tomomo086/3D_Storage_Box_System/Images/IMG_20250630_092257031.JPG

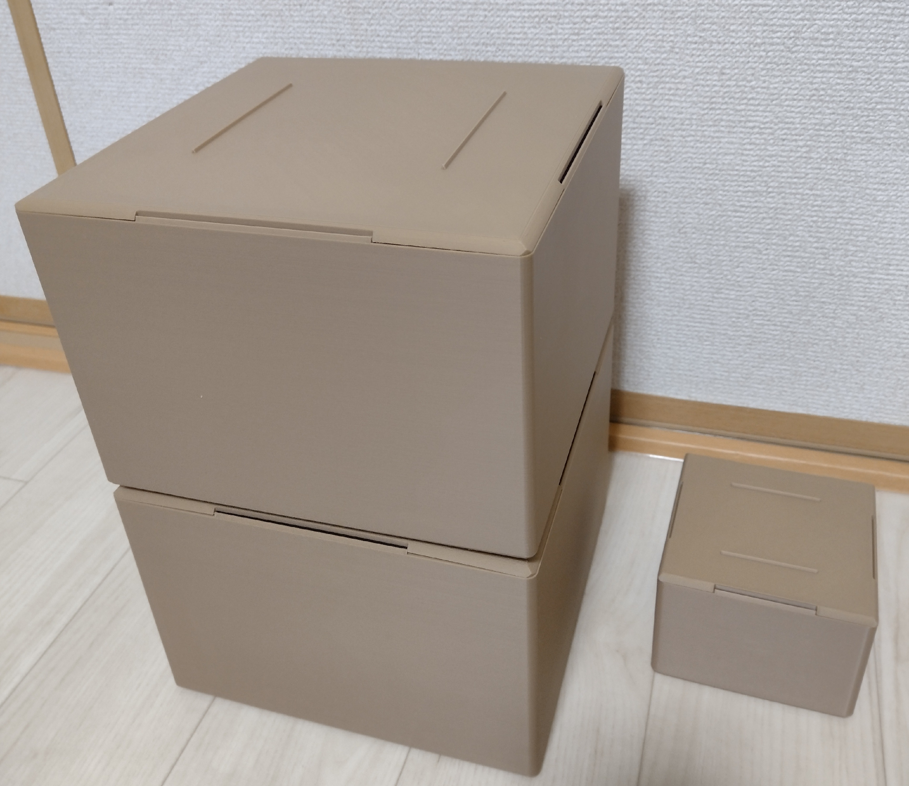
Images/IMG_20250630_092257031.JPG
